CrashOverride85/zc95/docs/images/AudioInput.png

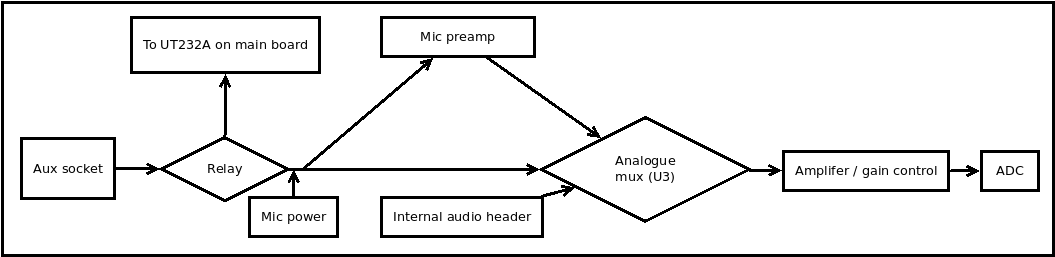
docs/images/AudioInput.png
