CrashOverride85/zc95/docs/images/screen_ra_menu.jpg

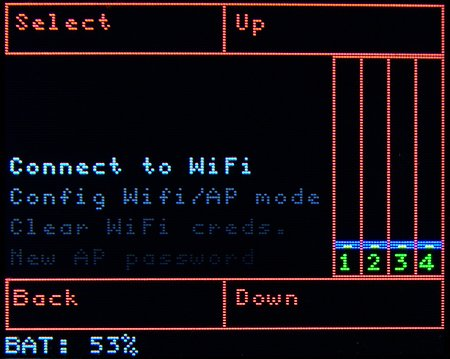
docs/images/screen_ra_menu.jpg
