CrashOverride85/zc95/source/zc95/PortExpanders/CMainBoardPortExp.h

#ifndef _CMAINBOARDPORTEXP_H
#define _CMAINBOARDPORTEXP_H

#include <stdio.h>
#include <cstdint>
#include "IPortExpander.h"
#include "../CGetButtonState.h"
#include "../ECButtons.h"
#include "../ZcTypes.h"

class CMainBoardPortExp : public CGetButtonState
{
    public:
        CMainBoardPortExp(zc95_version_t hardware_version, hw_variant_t mkII_variant, IPortExpander* port_exp);
        void process(bool always_update);
        bool button_state(enum Button button);
        bool has_button_state_changed(enum Button button, bool *new_state);
        void interrupt();
        void clear_input();
        void set_lcd_backlight(bool on);
        void audio_input_enable(bool enable);
        void mic_preamp_enable(bool enable);
        void mic_power_enable(bool enable);

        // MKII's with PCB >= v2.2 can route different signals to ADC0. For v2.0/2.1, it's always USB VBUS
        enum class adc0_select_t
        {
            USB_VBUS,
            USB_CC1,
            USB_CC2
        };

        void set_adc0_source(adc0_select_t source);

        bool get_tp4056_charge_status();
        bool get_tp4056_standby_status();

        void lcd_reset();
    
    private:
        uint8_t _last_read;
        uint8_t _button_states_at_last_check;
        uint8_t _address;
        int8_t _old_state;
        uint64_t _last_state_change[MAX_BUTTON_IDX];
        volatile bool _interrupt;
        zc95_version_t _hardware_version;
        hw_variant_t _mkII_variant;
        IPortExpander* _port_exp;

        const int MicPreampEnablePin = 4;
        const int MicPowerDisablePin = 5;

        // MK1 only
        const int AudioInputEnablePin = 6;
        const int BackLightPin = 7;

        // MK2.x only
        const int StandbyPin = 0;
        const int ChargePin = 1;

        // MK2.2+ only
        const int UsbCcSelectPin    = 2; // SW_SENSE1: High: select CC1, low: select CC2
        const int UsbSenseSelectPin = 3; // SW_SENSE2: High: sense USB VBUS, low: sense selected CC line (sense => send to Pico ADC0)
        const int LcdResetPin       = 7;
};

#endif
