CrashOverride85/zc95/source/zc95/core1/CRoutineOutputCore1.cpp

/*
 * ZC95
 * Copyright (C) 2021  CrashOverride85
 * 
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
 * You should have received a copy of the GNU General Public License
 * along with this program.  If not, see <http://www.gnu.org/licenses/>
 */

/* Includes functions to send messages to Core1, as well as processing
 * incoming messages from Core1
 */

#include "pico/multicore.h"
#include "pico/mutex.h"
#include <string.h>
#include <stdint.h>
#include <inttypes.h>


#include "../PortExpanders/EExtInputPort.h"
#include "CRoutineOutputCore1.h"
#include "Core1Messages.h"


CRoutineOutputCore1::CRoutineOutputCore1(CDisplay *display, CLedControl *led_control, IHal *hal, CAudio *audio)
{
    _display = display;
    _led_control = led_control;
    _hal = hal;
    _audio = audio;
}

void CRoutineOutputCore1::set_front_panel_power(uint8_t channel, uint16_t power)
{
    if (channel > MAX_CHANNELS)
        return;
    
    if (_front_pannel_power[channel] != power)
    {
        message msg = {0};
        msg.msg8[0] = MESSAGE_SET_FRONT_PANNEL_POWER;
        msg.msg8[1] = channel;
        msg.msg8[2] = power & 0xFF;
        msg.msg8[3] = (power >> 8) & 0xFF;

        _front_pannel_power[channel] = power;
        multicore_fifo_push_blocking(msg.msg32);
        update_display(channel);
    }
}

uint16_t CRoutineOutputCore1::get_output_power(uint8_t channel)
{
    if (channel >= MAX_CHANNELS)
        return 0;

    return _output_power[channel]; 
}

uint16_t CRoutineOutputCore1::get_front_pannel_power(uint8_t channel)
{
    if (channel >= MAX_CHANNELS)
        return 0;

    return _front_pannel_power[channel];
}

uint16_t CRoutineOutputCore1::get_max_output_power(uint8_t channel){
    if (channel >= MAX_CHANNELS)
        return 0;

    return _max_output_power[channel];
}

void CRoutineOutputCore1::activate_routine(uint8_t routine_id)
{
    message msg = {0};
    msg.msg8[0] = MESSAGE_ROUTINE_LOAD;
    msg.msg8[1] = routine_id;

    multicore_fifo_push_blocking(msg.msg32);
}

void CRoutineOutputCore1::stop_routine()
{
    message msg = {0};
    msg.msg8[0] = MESSAGE_ROUTINE_STOP;

    multicore_fifo_push_blocking(msg.msg32);
}

void CRoutineOutputCore1::set_remote_power(uint8_t channel, uint16_t power)
{
    if (channel > MAX_CHANNELS)
        return;
    
    if (_remote_power[channel] != power)
    {
        message msg = {0};
        msg.msg8[0] = MESSAGE_SET_REMOTE_ACCESS_POWER;
        msg.msg8[1] = channel;
        msg.msg8[2] = power & 0xFF;
        msg.msg8[3] = (power >> 8) & 0xFF;

        _remote_power[channel] = power;
        multicore_fifo_push_blocking(msg.msg32);
        update_display(channel);
    }
}

void CRoutineOutputCore1::enable_remote_power_mode()
{
    message msg = {0};
    msg.msg8[0] = MESSAGE_SET_REMOTE_ACCESS_MODE;
    msg.msg8[1] = 1;

    multicore_fifo_push_blocking(msg.msg32);
    _remote_mode_active = true;

    for (uint channel = 0; channel < MAX_CHANNELS; channel++)
        _display->set_power_level(channel, get_front_pannel_power(channel), get_output_power(channel), get_max_output_power(channel), _remote_mode_active);
}

void CRoutineOutputCore1::disable_remote_power_mode()
{
    message msg = {0};
    msg.msg8[0] = MESSAGE_SET_REMOTE_ACCESS_MODE;
    msg.msg8[1] = 0;

    multicore_fifo_push_blocking(msg.msg32);
    _remote_mode_active = false;

    for (uint channel = 0; channel < MAX_CHANNELS; channel++)
        _display->set_power_level(channel, get_front_pannel_power(channel), get_output_power(channel), get_max_output_power(channel), _remote_mode_active);
}

void CRoutineOutputCore1::update_display(uint8_t channel)
{
    _display->set_power_level(channel, get_front_pannel_power(channel), get_output_power(channel), get_max_output_power(channel), _remote_mode_active);
}

void CRoutineOutputCore1::menu_min_max_change(uint8_t menu_id, int16_t new_value)
{
    message msg = {0};
    msg.msg8[0] = MESSAGE_ROUTINE_MIN_MAX_CHANGE;
    msg.msg8[1] = menu_id;
    msg.msg8[2] = new_value & 0xFF;
    msg.msg8[3] = (new_value >> 8) & 0xFF;

    multicore_fifo_push_blocking(msg.msg32);
}

void CRoutineOutputCore1::menu_multi_choice_change(uint8_t menu_id, uint8_t choice_id)
{
    message msg = {0};
    msg.msg8[0] = MESSAGE_ROUTINE_MULTI_CHOICE_CHANGE;
    msg.msg8[1] = menu_id;
    msg.msg8[2] = choice_id & 0xFF;
    msg.msg8[3] = (choice_id >> 8) & 0xFF;

    multicore_fifo_push_blocking(msg.msg32);
}

void CRoutineOutputCore1::menu_selected(uint8_t menu_id)
{
    message msg = {0};
    msg.msg8[0] = MESSAGE_ROUTINE_MENU_SELECTED;
    msg.msg8[1] = menu_id;

    multicore_fifo_push_blocking(msg.msg32);
}

void CRoutineOutputCore1::trigger(trigger_socket socket, trigger_part part, bool active)
{
    message msg = {0};
    msg.msg8[0] = MESSAGE_ROUTINE_TRIGGER;
    msg.msg8[1] = (uint8_t)socket;
    msg.msg8[2] = (uint8_t)part;
    msg.msg8[3] = active;

    multicore_fifo_push_blocking(msg.msg32);
}

void CRoutineOutputCore1::soft_button_pressed(soft_button button, bool pressed)
{
    message msg = {0};
    msg.msg8[0] = MESSAGE_ROUTINE_SOFT_BUTTON_PUSHED;
    msg.msg8[1] = (uint8_t)button;
    msg.msg8[2] = pressed; // 1=pressed, 0=released

    multicore_fifo_push_blocking(msg.msg32);
}

void CRoutineOutputCore1::bluetooth_remote_passthrough(CBluetoothRemote::keypress_t key)
{
    message msg = {0};
    msg.msg8[0] = MESSAGE_BLUETOOTH_REMOTE_KEYPRESS;
    msg.msg8[1] = (uint8_t)key;

    multicore_fifo_push_blocking(msg.msg32);
}

void CRoutineOutputCore1::extended_ramp_start()
{
    message msg = {0};
    msg.msg8[0] = MESSAGE_EXTENDED_RAMP_START;

    multicore_fifo_push_blocking(msg.msg32);
}

void CRoutineOutputCore1::loop()
{
    // Process inbound messages from Core1
    while (multicore_fifo_rvalid())
    {
        message msg;
        msg.msg32 = multicore_fifo_pop_blocking();
        // printf("CRoutineOutputCore1::loop(): get message (%d\t%d\t%d\t%d\n", msg.msg8[0], msg.msg8[1], msg.msg8[2], msg.msg8[3]);
        process_message(msg);
    }

    process_text_message_queue();
}

// Process message received from core1
void CRoutineOutputCore1::process_message(message msg)
{
    switch(msg.msg8[0])
    {
        case MESSAGE_SET_DISPLAY_POWER:
        {
            uint8_t channel = msg.msg8[1];
            uint16_t power = msg.msg8[2];
            power |= msg.msg8[3] << 8;
            
            if (channel >= MAX_CHANNELS)
                return;
            
            _output_power[channel] = power;
            update_display(channel);
            break;
        }

        case MESSAGE_SET_MAXIMUM_POWER:
        {
            uint8_t channel = msg.msg8[1];
            uint16_t power = msg.msg8[2];
            power |= msg.msg8[3] << 8;
            
            if (channel >= MAX_CHANNELS)
                return;
            
            _max_output_power[channel] = power;
            update_display(channel);
            break;
        }

        case MESSAGE_SET_LED_CHAN0:
        case MESSAGE_SET_LED_CHAN1:
        case MESSAGE_SET_LED_CHAN2:
        case MESSAGE_SET_LED_CHAN3:
        {
            uint8_t led_chan = msg.msg8[0] - MESSAGE_SET_LED_CHAN0;
            if (led_chan > 3)
            {
                printf("Unexpected led chan id of %d\n", led_chan);
            }

            LED led;
            switch(led_chan)
            {
                case 0: led = LED::Channel1; break;
                case 1: led = LED::Channel2; break;
                case 2: led = LED::Channel3; break;
                case 3: led = LED::Channel4; break;
                default: return;
            }

            uint8_t red   = msg.msg8[1];
            uint8_t green = msg.msg8[2];
            uint8_t blue  = msg.msg8[3];

            uint32_t colour = blue | (green << 8) | (red << 16); 
            _led_control->set_led_colour(led, colour);
            break;
        }

        case MESSAGE_SET_ACC_IO_PORT1_STATE:
            set_acc_io_port_state(ExtInputPort::ACC_IO_1, (ExtInputPortState)msg.msg8[1]);
            break;

        case MESSAGE_SET_ACC_IO_PORT2_STATE:
            set_acc_io_port_state(ExtInputPort::ACC_IO_2, (ExtInputPortState)msg.msg8[1]);
            break;

        case MESSAGE_SET_ACC_IO_PORT3_STATE:
            set_acc_io_port_state(ExtInputPort::ACC_IO_3, (ExtInputPortState)msg.msg8[1]);
            break;

        case MESSAGE_SET_ACC_IO_PORT_RESET:
            reset_acc_port();
            break;

        case MESSAGE_LUA_SCRIPT_STATE:
            _lua_script_state = (lua_script_state_t)msg.msg8[1];
            break;

        case MESSAGE_SET_AUDIO_MODE:
            _audio->set_audio_mode((audio_mode_t)msg.msg8[1]);
            break;

        case MESSAGE_SET_MENU_VALUE:
            {
                if (_menu_change_callback == NULL) 
                    break;

                menu_change_msg_t menu_change_msg;
                menu_change_msg.menu_id = msg.msg8[1];
                menu_change_msg.new_value  = msg.msg8[2];
                menu_change_msg.new_value |= msg.msg8[3] << 8;

                _menu_change_callback(menu_change_msg);
            }
            break;

        case MESSAGE_EXTENDED_RAMP_PROGRESS:
        {
            uint8_t percent = msg.msg8[1];
            uint16_t seconds_remaining = msg.msg8[2];
            seconds_remaining |= msg.msg8[3] << 8;
            _display->set_extended_ramp_progress(percent, seconds_remaining);
            break;
        }
    }
}

void CRoutineOutputCore1::process_text_message_queue()
{
    uint8_t count = 0;
    pattern_text_output_t text_message;
    memset(&text_message, 0, sizeof(text_message));

    // Get at most 5 messages from queue, to prevent a flood of print() messages from lua 
    // effectively locking us up
    while (queue_try_remove(&gPatternTextOutputQueue, &text_message) && count++ < 5)
    {
        if (_text_output_callback != NULL)
            _text_output_callback(text_message);
    }
}

void CRoutineOutputCore1::collar_transmit (uint16_t id, CCollarComms::collar_channel channel, CCollarComms::collar_mode mode, uint8_t power)
{
    // Shove the collar message in global variable protected by a mutex, then send 
    // a message on the FIFO queue to tell core1 there's a message to be sent
    if (multicore_fifo_wready())
    {
        if (mutex_enter_timeout_ms(&g_collar_message_mutex, 100))
        {
            g_collar_message.channel = channel;
            g_collar_message.mode = mode;
            g_collar_message.id = id;
            g_collar_message.power = power;

            message msg = {0};
            msg.msg8[0] = MESSAGE_TRIGGER_COLLAR;
            msg.msg8[1] = 0;
            msg.msg8[2] = 0;
            msg.msg8[3] = 0;

            mutex_exit(&g_collar_message_mutex);
            multicore_fifo_push_blocking(msg.msg32);       
        }
        else
        {
            printf("collar_transmit(): Unable to obtain mutex\n");
        }
    }
    else
    {
        printf("collar_transmit(): FIFO queue to core1 full\n");
    }
}

void CRoutineOutputCore1::reinit_channels()
{
    message msg = {0};
    msg.msg8[0] = MESSAGE_REINIT_CHANNELS;
    msg.msg8[1] = 0;
    msg.msg8[2] = 0;
    msg.msg8[3] = 0;

    multicore_fifo_push_blocking(msg.msg32);
}

void CRoutineOutputCore1::suspend_core1()
{
    message msg = {0};
    msg.msg8[0] = MESSAGE_CORE1_SUSPEND;
    msg.msg8[1] = 0;
    msg.msg8[2] = 0;
    msg.msg8[3] = 0;

    multicore_fifo_push_blocking(msg.msg32);
}

void CRoutineOutputCore1::audio_threshold_reached(uint16_t fundamental_freq, uint8_t cross_count)
{
    message msg = {0};
    msg.msg8[0] = MESSAGE_AUDIO_THRES_REACHED;
    msg.msg8[1] = fundamental_freq & 0xFF;
    msg.msg8[2] = (fundamental_freq >> 8) & 0xFF;
    msg.msg8[3] = cross_count;

    multicore_fifo_push_blocking(msg.msg32);
}

void CRoutineOutputCore1::audio_intensity_change(uint8_t left_chan, uint8_t right_chan, uint8_t virt_chan)
{
    message msg = {0};
    msg.msg8[0] = MESSAGE_AUDIO_INTENSITY;
    msg.msg8[1] = left_chan;
    msg.msg8[2] = right_chan;
    msg.msg8[3] = virt_chan;

    multicore_fifo_push_blocking(msg.msg32);
}

void CRoutineOutputCore1::reset_acc_port()
{
    if (_hal)
        _hal->acc_port_reset();
}

void CRoutineOutputCore1::set_acc_io_port_state(ExtInputPort output, ExtInputPortState state)
{
    if (_hal)
        _hal->acc_port_set_io_port_state(output, state);
}

lua_script_state_t CRoutineOutputCore1::get_lua_script_state()
{
    return _lua_script_state;
}

void CRoutineOutputCore1::set_text_callback_function(std::function<void(pattern_text_output_t)> cb)
{
    _text_output_callback = cb;
}

void CRoutineOutputCore1::set_menu_change_callback_function(std::function<void(menu_change_msg_t)> cb)
{
    _menu_change_callback = cb;
}
